darkosancanin/avr_pong/gabriella_and_charlotte.cpp

#include "gabriella_and_charlotte.h"

PROGMEM const unsigned char gabriella_and_charlotte[] = {
120,96,
0xFF,0xFF,0x00,0x3F,0xF8,0x38,0x3F,0xFF,0xFF,0xFF,0xFF,0xFF,0xFF,0xFF,0xFF,
0xFF,0xFC,0x00,0x27,0xFE,0x1C,0x1F,0xFF,0xFF,0xFF,0xFF,0xFF,0xFF,0xFF,0xFF,
0xFF,0xF8,0x00,0x63,0xFF,0x0C,0x0F,0xFF,0xFF,0xFF,0xFF,0xFF,0xFF,0xFF,0xFF,
0xFF,0xF0,0x00,0x7F,0xFF,0xFE,0x07,0xFF,0xFF,0xFF,0xFF,0xFF,0xFF,0xFF,0xFF,
0xFF,0xF0,0x00,0xFF,0xFF,0xFF,0x83,0xFF,0xFF,0xFF,0xFF,0xFF,0xFF,0xFF,0xFF,
0xFF,0xF0,0x43,0xFF,0xFF,0xFF,0xC0,0x7F,0xFF,0xFF,0xFF,0xFF,0xFF,0xFF,0xFF,
0xFF,0xF0,0x7F,0xFF,0xFF,0xFF,0xF0,0x7F,0xFF,0xFF,0xFF,0xFF,0xFF,0xFF,0xFF,
0xFF,0xE0,0x7F,0xFF,0xFF,0xFF,0xCE,0x3F,0xF7,0xFF,0xFF,0xFF,0xFF,0xFF,0xFF,
0xFF,0xE0,0x7F,0xFF,0xFF,0xFF,0xC2,0x1F,0xFF,0xFF,0xFF,0xFF,0xFF,0xFF,0xFF,
0xFF,0xC0,0x3F,0xFF,0xFF,0xFF,0xE0,0x1F,0xFF,0xFF,0xFF,0xFF,0xFF,0xFF,0xFF,
0xFF,0xC0,0x1F,0xFF,0xFF,0xFF,0xF0,0x07,0xFF,0xFF,0xFF,0xFF,0xFF,0xFF,0xFF,
0xFF,0x80,0x1F,0xFF,0xFF,0xFF,0xF4,0x07,0xFF,0xFF,0xFF,0xFF,0xFF,0xFF,0xFF,
0xFF,0x80,0x1F,0xFF,0xFF,0xFF,0xF0,0x03,0xFF,0xFF,0xFF,0xFF,0xFF,0xFF,0xFF,
0xFF,0x00,0x1F,0xFF,0xFF,0xFF,0xF0,0x03,0xFF,0xFF,0xFF,0xFF,0xFF,0xFF,0xFF,
0xFF,0x00,0x1F,0xFF,0xF9,0xFF,0xF8,0x01,0x7F,0xFF,0xFF,0xFF,0xFF,0xFF,0xFF,
0xFF,0x80,0x00,0x3F,0xFF,0xFF,0xF8,0x00,0x7F,0xFF,0xFF,0xFF,0xFF,0xFF,0xFF,
0xFF,0x80,0x00,0x1F,0xFE,0x0F,0xF0,0x00,0xBF,0xFF,0xFF,0xFF,0xFF,0xFF,0xFF,
0xFF,0x80,0x18,0x0F,0xF8,0x01,0xF0,0x00,0x3F,0xFF,0xFF,0xFF,0xFF,0xFF,0xFF,
0xFF,0x80,0x30,0x0F,0xF1,0x00,0xF8,0x00,0x3F,0xFF,0xFF,0xFF,0xFF,0xFF,0xFF,
0xFF,0xC0,0x00,0x07,0xF9,0x0F,0xF8,0x00,0x3F,0xFF,0xFF,0xFF,0xFF,0xFF,0xFF,
0xFF,0xC0,0x00,0x07,0xFF,0xFF,0xF8,0x00,0x1F,0xFF,0xFF,0xFF,0x7F,0xFF,0xFF,
0xFF,0x80,0x04,0x07,0xFF,0xFF,0xF8,0x00,0x1F,0xFF,0xFF,0xFF,0xFF,0xFF,0xFF,
0xFF,0x00,0x00,0x4F,0xFF,0xFF,0xF8,0x00,0x1F,0xFF,0x42,0xFF,0xFF,0xFF,0xFF,
0xFF,0x00,0x06,0x1F,0xFF,0xFF,0xFC,0x00,0x1F,0x7F,0x00,0x7F,0xFF,0xFF,0xFF,
0xFF,0x00,0x70,0xFF,0xFF,0xFF,0xFC,0x00,0x1E,0x30,0x00,0x0F,0xFF,0xFF,0xFF,
0xFF,0x00,0x7F,0xFF,0xFF,0xFF,0xFD,0x00,0x5F,0xE0,0x00,0x0F,0xFF,0xFF,0xFF,
0xFF,0x00,0xFF,0xFF,0xFF,0xFF,0xFE,0x00,0x9F,0xE0,0x00,0x0F,0xFF,0xFF,0xFF,
0xFF,0x00,0x7F,0xFF,0xFF,0xFF,0xFE,0x02,0x7F,0xF0,0x1F,0xEF,0xFF,0xFF,0xFF,
0xFF,0x80,0x7F,0xF3,0xCF,0xFF,0xFE,0x00,0xFF,0xE0,0x37,0xF3,0xFF,0xFF,0xFF,
0xFF,0x80,0x7F,0xF1,0xCF,0xFF,0xFC,0x03,0xFF,0xE0,0x33,0xF3,0xCE,0xFF,0xFF,
0xFF,0x00,0x7F,0xE0,0x7F,0xFF,0xFC,0x1F,0xFF,0xFC,0xFF,0xFE,0x07,0x7F,0xFF,
0xFF,0x00,0x3F,0xC3,0xFF,0xBF,0xFD,0x1F,0xFF,0xFF,0xFF,0xFF,0x01,0xFF,0xFF,
0xFF,0x80,0x7F,0xF3,0xFF,0x8F,0xFD,0x3F,0xFF,0x8F,0xFF,0xFF,0xE1,0xFF,0xFF,
0xFF,0x80,0x5F,0xFF,0xFF,0xC7,0xFC,0x7F,0xFF,0x9F,0xFF,0xFF,0xF9,0x3F,0xFF,
0xFF,0x80,0x0F,0x9F,0xFF,0xC3,0xFC,0xFF,0xFE,0x1E,0xFF,0xFD,0xFC,0x5F,0xFF,
0xFF,0x80,0x07,0x0C,0x00,0x07,0xFC,0xFF,0xF8,0x20,0x4A,0x3F,0xF8,0x6F,0xFF,
0xFF,0x80,0x07,0x00,0x00,0x3F,0xF9,0xFF,0xF0,0x3E,0x6E,0x7F,0xF8,0x23,0xFF,
0xFF,0x00,0x07,0x80,0x71,0xFF,0xF3,0xFF,0xC8,0x00,0x7F,0xC1,0xF0,0x03,0xFF,
0xFF,0xC0,0x07,0xC1,0xCF,0xFF,0xE3,0xF6,0x00,0x00,0x1F,0xFE,0x70,0x03,0xFF,
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
};
