darkosancanin/avr_pong/pong_logo.cpp

#include "pong_logo.h"

PROGMEM const unsigned char pong_logo[] = {
96,21,
0xFF,0xFF,0xC0,0x3F,0xFF,0xFE,0x1E,0x00,0x0F,0x0F,0xFF,0xFF,
0xFF,0xFF,0xE0,0x3F,0xFF,0xFE,0x1E,0x00,0x0F,0x0F,0xFF,0xFF,
0xFF,0xFF,0xF0,0x3F,0xFF,0xFE,0x1F,0x00,0x0F,0x0F,0xFF,0xFF,
0xFF,0xFF,0xF8,0x3F,0xFF,0xFE,0x1F,0x80,0x0F,0x0F,0xFF,0xFF,
0xF0,0x00,0x78,0x3C,0x00,0x1E,0x1F,0xC0,0x0F,0x0F,0x00,0x00,
0xF0,0x00,0x78,0x3C,0x00,0x1E,0x1F,0xE0,0x0F,0x0F,0x00,0x00,
0xF0,0x00,0x78,0x3C,0x00,0x1E,0x1F,0xF0,0x0F,0x0F,0x00,0x00,
0xF0,0x00,0x78,0x3C,0x00,0x1E,0x1F,0xF8,0x0F,0x0F,0x00,0x00,
0xFF,0xFF,0xF8,0x3C,0x00,0x1E,0x1E,0xFC,0x0F,0x0F,0x0F,0xFF,
0xFF,0xFF,0xF8,0x3C,0x00,0x1E,0x1E,0x7E,0x0F,0x0F,0x0F,0xFF,
0xFF,0xFF,0xF8,0x3C,0x00,0x1E,0x1E,0x3F,0x0F,0x0F,0x0F,0xFF,
0xFF,0xFF,0xF8,0x3C,0x00,0x1E,0x1E,0x1F,0x8F,0x0F,0x0F,0xFF,
0xF0,0x00,0x00,0x3C,0x00,0x1E,0x1E,0x0F,0xCF,0x0F,0x00,0x0F,
0xF0,0x00,0x00,0x3C,0x00,0x1E,0x1E,0x07,0xEF,0x0F,0x00,0x0F,
0xF0,0x00,0x00,0x3C,0x00,0x1E,0x1E,0x03,0xFF,0x0F,0x00,0x0F,
0xF0,0x00,0x00,0x3C,0x00,0x1E,0x1E,0x01,0xFF,0x0F,0x00,0x0F,
0xF0,0x00,0x00,0x3C,0x00,0x1E,0x1E,0x00,0xFF,0x0F,0x00,0x0F,
0xF0,0x00,0x00,0x3F,0xFF,0xFE,0x1E,0x00,0x7F,0x0F,0xFF,0xFF,
0xF0,0x00,0x00,0x3F,0xFF,0xFE,0x1E,0x00,0x3F,0x0F,0xFF,0xFF,
0xF0,0x00,0x00,0x3F,0xFF,0xFE,0x1E,0x00,0x1F,0x0F,0xFF,0xFF,
0xF0,0x00,0x00,0x3F,0xFF,0xFE,0x1E,0x00,0x0F,0x0F,0xFF,0xFF
};
